CubanJew/msfs20_custom_spad_controller/resources/_FINAL - Side VIew.jpg

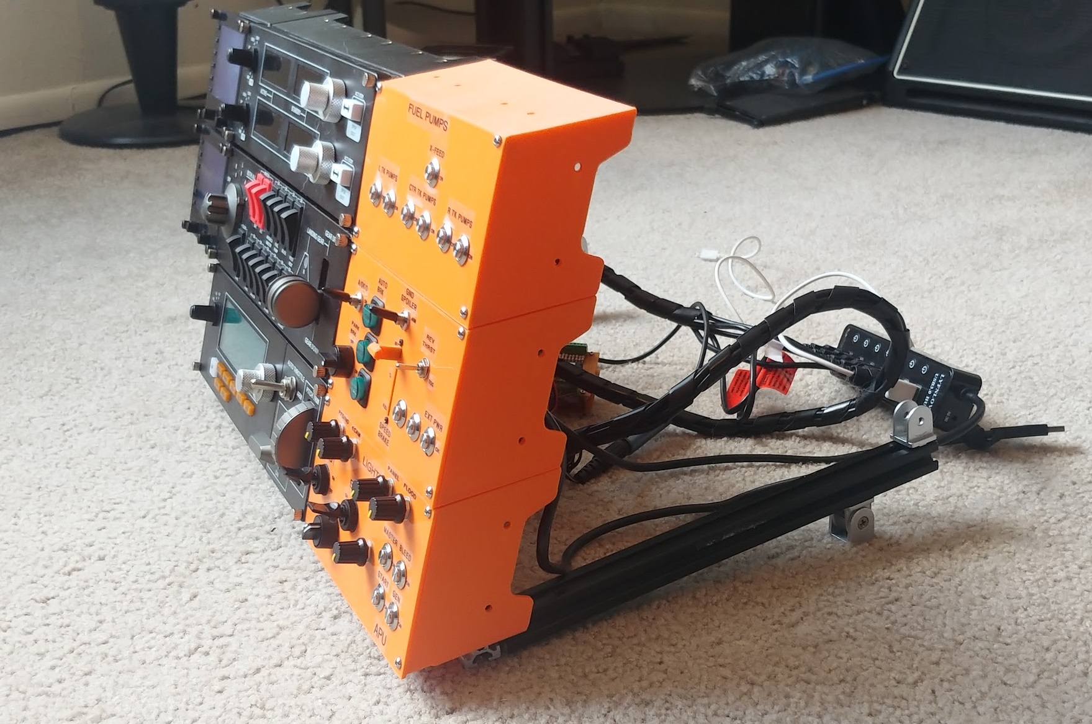
resources/_FINAL - Side VIew.jpg
