CubanJew/msfs20_custom_spad_controller/resources/Enclosure Box-Final.jpg

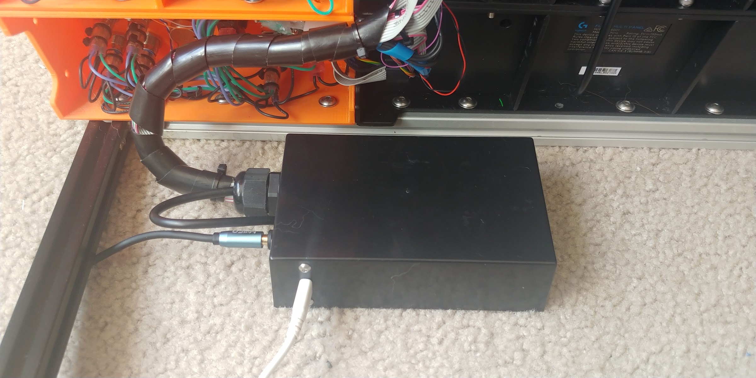
resources/Enclosure Box-Final.jpg
