CubanJew/msfs20_custom_spad_controller/resources/Prototype - Breadboard 1.jpg

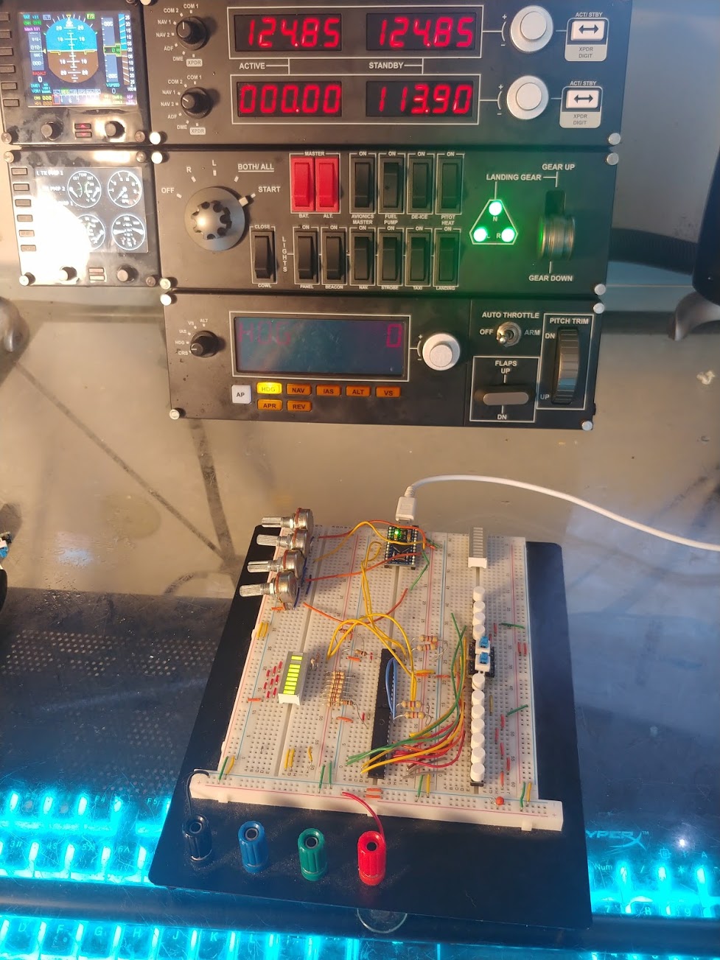
resources/Prototype - Breadboard 1.jpg
