CubanJew/msfs20_custom_spad_controller/resources/Prototype - Breadboard 2.jpg

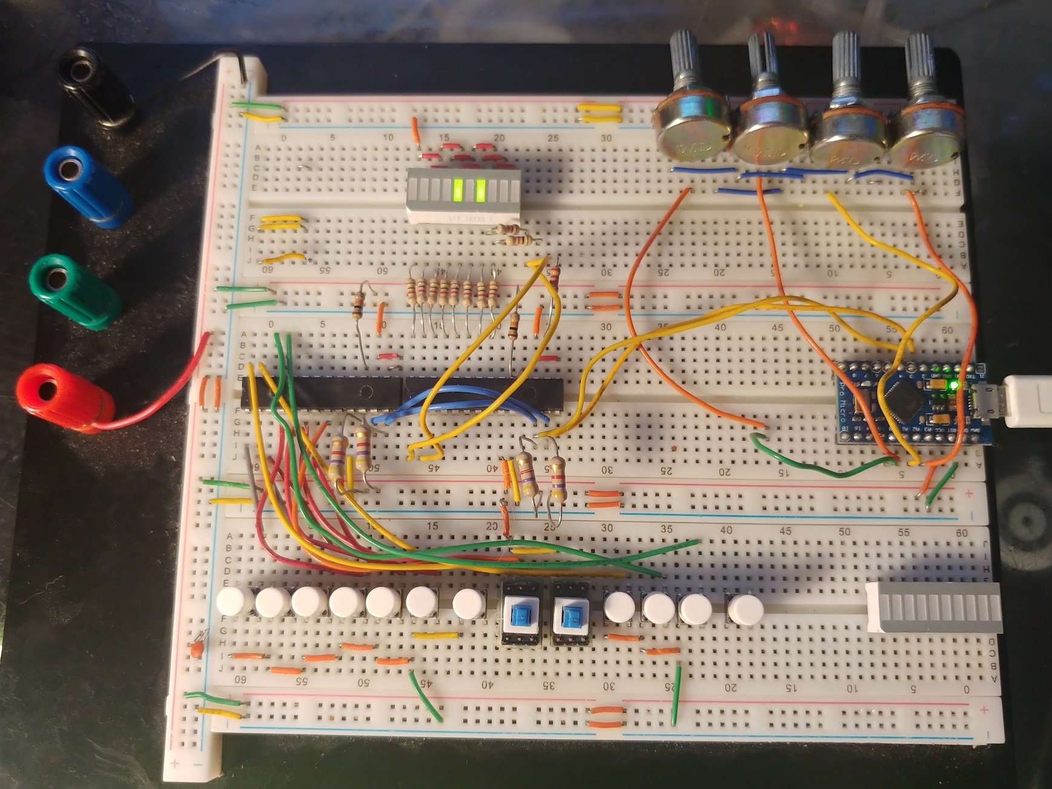
resources/Prototype - Breadboard 2.jpg
