CubanJew/msfs20_custom_spad_controller/resources/Back View - Getting Started.jpg

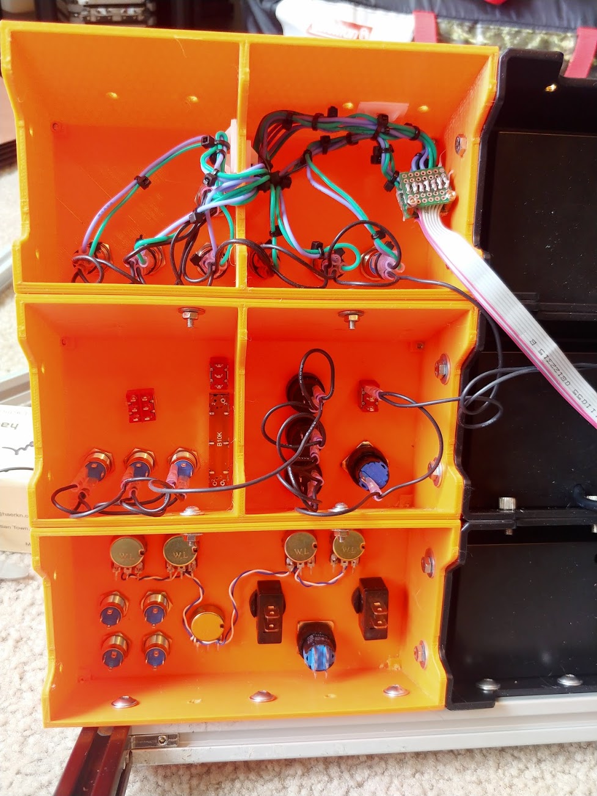
resources/Back View - Getting Started.jpg
